j-hoppe/QUniBone/10.01_base/2_src/pru1_u/pru1_statemachine_data_slave.c

/* pru1_statemachine_data_slave.c: state machine for execution of slave DATO* or DATI* cycles

 Copyright (c) 2018-2019, Joerg Hoppe
 j_hoppe@t-online.de, www.retrocmp.com

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

 29-jun-2019	JH		rework: state returns ptr to next state func
 12-nov-2018  JH      entered beta phase

 Statemachine for execution of slave DATO* or DATI* cycles.
 All references "PDP11BUS handbook 1979"

 Slave reponds not to INIT on this level, master must stop bus transactions.

 - Slave waits for MSYN L->H
 - slaves fetches address and control lines
 - address is evaluated, ggf mem access
 */

#include <stdlib.h>
#include <stdint.h>

#include "pru1_utils.h"

#include "mailbox.h"
#include "ddrmem.h"
#include "iopageregister.h"

#include "pru1_buslatches.h"
#include "pru1_statemachine_data_slave.h"

// forwards ;
//statemachine_state_func sm_data_slave_start(void);
static statemachine_state_func sm_data_slave_state_10(void);
static statemachine_state_func sm_data_slave_state_20(void);
//static statemachine_state_func sm_data_slave_state_99(void);

// check for MSYN active
statemachine_state_func sm_data_slave_start() {
	uint8_t latch2val, latch3val, latch4val;
	// uint8_t iopage;
	uint32_t addr;
	uint8_t control;
	uint16_t data;
	// uint8_t	page_table_entry ;
	uint16_t w;
	uint8_t b;

	// fast sample of busstate, should be atomic
	latch4val = buslatches_getbyte(4); // MSYN first

	// MSYN active ?
	if (!(latch4val & BIT(4)))
		return NULL; // still idle
	if (latch4val & BIT(5))
		// SSYN active: cycle answered by other bus slave
		return NULL; // still idle
	// checking against SSYN guarantees address if valid if fetched now.
	// However, another Bus slave can SSYN immediately

	latch2val = buslatches_getbyte(2); // A0..7
	latch3val = buslatches_getbyte(3); // A8..15

	// decode address and control
	// addr0..7 = latch[2]
	// addr8..15 = latch[3]
	// addr 16,17 = latch[4].0,1
	addr = latch2val | ((uint32_t) latch3val << 8) | ((uint32_t) (latch4val & 3) << 16);
	
	// make bool of a17..a13. iopage, if a17..a13 all 1's
	// iopage = ((latch3val & 0xe0) | (latch4val & 3)) == 0xe3;
	// 2 statements above = 12 cycles = 60ns

	// C0 = latch[4], bit 2
	// C1 = latch[4], bit 3
	control = (latch4val >> 2) & 3;
	// !!! Attention: on fast UNIBUS cycles to other devices,
	// !!! SSYN may already be asserted. Or MSYN may even be inactive again !!!

//	if (addr == 0 && control == QUNIBUS_CYCLE_DATI) // trigger address, after boot
//	  PRU_DEBUG_PIN0(1) ; // trigger to LA.
//if (addr >= 0777560 && addr <= 0777566) // trigger address, after boot
//	PRU_DEBUG_PIN0(1) ; // trigger to LA.


	// page_table_entry = PAGE_TABLE_ENTRY(pru_iopage_registers,addr) ; // is addr ignored,memory,iopage?
//	if (addr >= 0x8000 && addr < 0x10000)
//		page_table_entry = PAGE_MEMORY ;
	switch (control) {
	case QUNIBUS_CYCLE_DATI: // fast cases first
	case QUNIBUS_CYCLE_DATIP:
		// DATI: get data from memory or registers onto BUS, then SSYN
		if (emulated_addr_read(addr, &data)) {

			// DATA[0..7] = latch[5]
			buslatches_setbyte(5, data & 0xff);
			// DATA[8..15] = latch[6]
			buslatches_setbyte(6, data >> 8);
			// set SSYN = latch[4], bit 5
			buslatches_setbits(4, BIT(5), BIT(5));
			return (statemachine_state_func) &sm_data_slave_state_20;
			// perhaps PRU2ARM_INTERRUPT now active
		} else
			// no address match: wait for MSYN to go inactive
			// return (statemachine_state_func) &sm_data_slave_state_99;
			return NULL ;
	case QUNIBUS_CYCLE_DATO:
		// fetch data in any case
		// DATA[0..7] = latch[5]
		w = buslatches_getbyte(5);
		// DATA[8..15] = latch[6]
		w |= (uint16_t) buslatches_getbyte(6) << 8;
		if (emulated_addr_write_w(addr, w)) {

			// SSYN = latch[4], bit 5
			buslatches_setbits(4, BIT(5), BIT(5));
			// wait for MSYN to go inactive, then SSYN inactive
			return (statemachine_state_func) &sm_data_slave_state_10;
			// perhaps PRU2ARM_INTERRUPT now active
		} else
			// no address match: wait for MSYN to go inactive
			// return (statemachine_state_func) &sm_data_slave_state_99;
			return NULL ;
	case QUNIBUS_CYCLE_DATOB:
		// A00 = 1, odd address: get upper byte
		// A00 = 0: even address, get lower byte
		// fetch data
		if (addr & 1) {
			// DATA[8..15] = latch[6]
			b = buslatches_getbyte(6);
		} else {
			// DATA[0..7] = latch[5]
			b = buslatches_getbyte(5);
		}
		if (emulated_addr_write_b(addr, b)) { // always sucessful, addr already tested
			// SSYN = latch[4], bit 5
			buslatches_setbits(4, BIT(5), BIT(5));
			// wait for MSYN to go inactive, then SSYN inactive
			return (statemachine_state_func) &sm_data_slave_state_10;
			// perhaps PRU2ARM_INTERRUPT now active
		} else
			// no address match: wait for MSYN to go inactive
			// return (statemachine_state_func) &sm_data_slave_state_99;
			return NULL ;
	}
	return NULL; // not reached
}

// End DATO: wait for MSYN to go inactive, then SSYN inactive
// also wait for EVENT ACK
static statemachine_state_func sm_data_slave_state_10() {
	// MSYN = latch[4], bit 4
	if (buslatches_getbyte(4) & BIT(4))
		return (statemachine_state_func) &sm_data_slave_state_10; // wait, MSYN still active
	if (! EVENT_IS_ACKED(mailbox,deviceregister))
		// unibusadapter.worker() did not yet run on_after_register_access() 
		// => wait, long SSYN delay until ARM acknowledges event
		return (statemachine_state_func) &sm_data_slave_state_10;
	// if ARM was triggered by event and changed the device state,
	// now an Interrupt arbitration may be pending.

	// clear SSYN = latch[4], bit 5
	buslatches_setbits(4, BIT(5), 0);

	return NULL; // ready 
}

// End DATI: wait for MSYN to go inactive, then SSYN and DATA inactive
// also wait for EVENT ACK
static statemachine_state_func sm_data_slave_state_20() {
	// MSYN = latch[4], bit 4
	if (buslatches_getbyte(4) & BIT(4))
		return (statemachine_state_func) &sm_data_slave_state_20; // wait, MSYN still active
	if (! EVENT_IS_ACKED(mailbox,deviceregister))
		// unibusadapter.worker() did not yet run on_after_register_access() 
		// => wait, long SSYN delay until ARM acknowledges event
		return (statemachine_state_func) &sm_data_slave_state_20;
	// if ARM was triggered by event and changed the device state,
	// now an Interrupt arbitration may be pending.

	// clear first data, then SSYN
	// DATA[0..7] = latch[5]
	buslatches_setbyte(5, 0);
	// DATA[8..15] = latch[6]
	buslatches_setbyte(6, 0);
	// clear SSYN = latch[4], bit 5
	buslatches_setbits(4, BIT(5), 0);
	return NULL; // ready 
}


// end of inactive cycle: wait for MSYN to go inactive
// Not necessary, start() state simply checks addr again if MSYN still set.
static statemachine_state_func sm_data_slave_state_99() {
	// MSYN = latch[4], bit 4
	if (buslatches_getbyte(4) & BIT(4)) {
		return (statemachine_state_func) &sm_data_slave_state_99; // wait, MSYN still active
	}
	return NULL; // ready
}
