j-hoppe/QUniBone/10.02_devices/2_src/rx0102drive.hpp

/* rx0102drive.hpp: implementation of RX01/RX02 disk drive, attached to RX0102 uCPU

 Copyright (c) 2020, Joerg Hoppe
 j_hoppe@t-online.de, www.retrocmp.com

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
 10-jan-2020  JH      start

 The microCPU board contains all logic and state for the RX01/02 subsystem.
 It is connected on one side two to "dump" electro-mechanical drives,
 on the other side two a RX11/RXV11/RX211/RXV21 UNIBUS/QBUS interface.
 */
#ifndef _RX0102DRIVE_HPP_
#define _RX0102DRIVE_HPP_

#include <stdint.h>
#include <string.h>
#include <vector>

#include "storagedrive.hpp"


class RX0102uCPU_c;
class RX0102drive_c: public storagedrive_c {
private:

    volatile unsigned cylinder; // current head position

public:
	static const unsigned cylinder_count_const = 77 ; // for array declaration 
	static const unsigned sector_count_const = 26 ;
	
	
    // the RX11 controller may see everything
    // dynamic state
    bool is_RX02 ; // false: RX01, true: FM/MFM RX02 drive
    bool double_density ; // true = RX02 and MFM

    unsigned full_rpm = 360; // normal rotation speed
    // track-to-track time is 5ms, head settle is 25ms
    unsigned track_step_time_ms = 5 ;
    // disk is always spinning
    unsigned head_settle_time_ms = 25 ;

    unsigned get_cylinder() ;
    void set_cylinder(unsigned cyl) ;

    bool error_illegal_track  ;
    bool error_illegal_sector ;

    parameter_string_c density_name = parameter_string_c(this, "density", "d",/*readonly*/
                                      false, "SD for RX01 & RX02 FM; DD for RX02 MFM");

    parameter_bool_c imagetrack0 = parameter_bool_c(this, "imagetrack0", "it0",/*readonly*/
                                   false, "true: File image contains track 0-76 (std), else only 1..76");

    // current head position , info only
    parameter_unsigned_c current_track = parameter_unsigned_c(this, "track", "tr", /*readonly*/
                                         true, "", "%d", "Track # of current head position", 77, 10);

private:

    // IBM floppy format allows a "delete mark" for each sector.
    // DEC : "Delete data mark is not used during normal operation,
    // but the RX01 can identify and write deleted data marks under program control,
    // The deleted data mark is only included in the RX11 to be IBM compatible."
    //
    // These sector marks are persistent on the floppy disk, but not saved in the
    // SimH-compatible image file format.
    // To pass the ZRX* diags, sector marks are held volatile "per drive".
    bool deleted_data_marks[cylinder_count_const][sector_count_const] ;


    bool check_disk_address(unsigned track, unsigned sector) ;

public:
    RX0102uCPU_c *uCPU ; // link to micro CPU board

    // no user controls!

    RX0102drive_c(RX0102uCPU_c *uCPU, bool is_RX02);

    bool on_param_changed(parameter_c *param) override;

    void on_power_changed(signal_edge_enum aclo_edge, signal_edge_enum dclo_edge) override;
    void on_init_changed(void) override;

    unsigned get_rotation_ms() ;

    // door closed, flopyp inserted?
    bool check_ready(void) ;

    void set_density(bool double_density);

    int get_sector_image_offset(unsigned track, unsigned sector) ;
    bool sector_read(uint8_t *sector_buffer, bool *deleted_data_mark, unsigned track, unsigned sector, bool with_delay) ;
    bool sector_write(uint8_t *sector_buffer, bool deleted_data_mark, unsigned track, unsigned sector, bool with_delay) ;


    // background worker function
    void worker(unsigned instance) override;
};

#endif
